50an6xy06r6n/hotswap_pcb_generator/img/gallery/pcb_composite.png

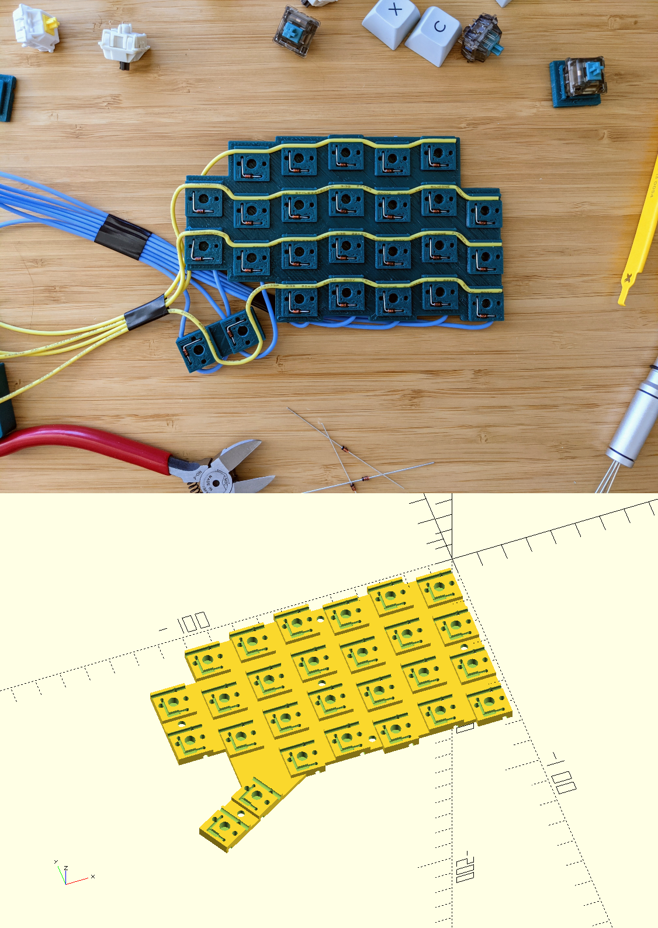
img/gallery/pcb_composite.png
