50an6xy06r6n/hotswap_pcb_generator/img/gallery/solid_case.jpg

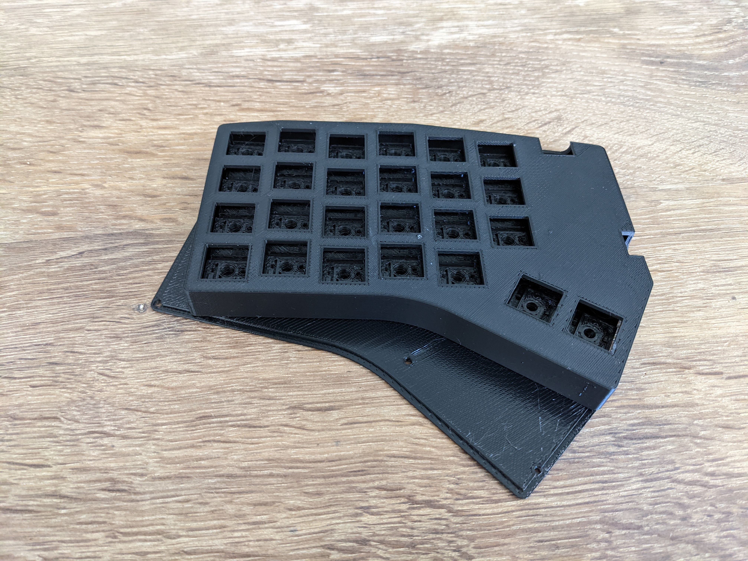
img/gallery/solid_case.jpg
