50an6xy06r6n/hotswap_pcb_generator/img/gallery/stabilizer.jpg

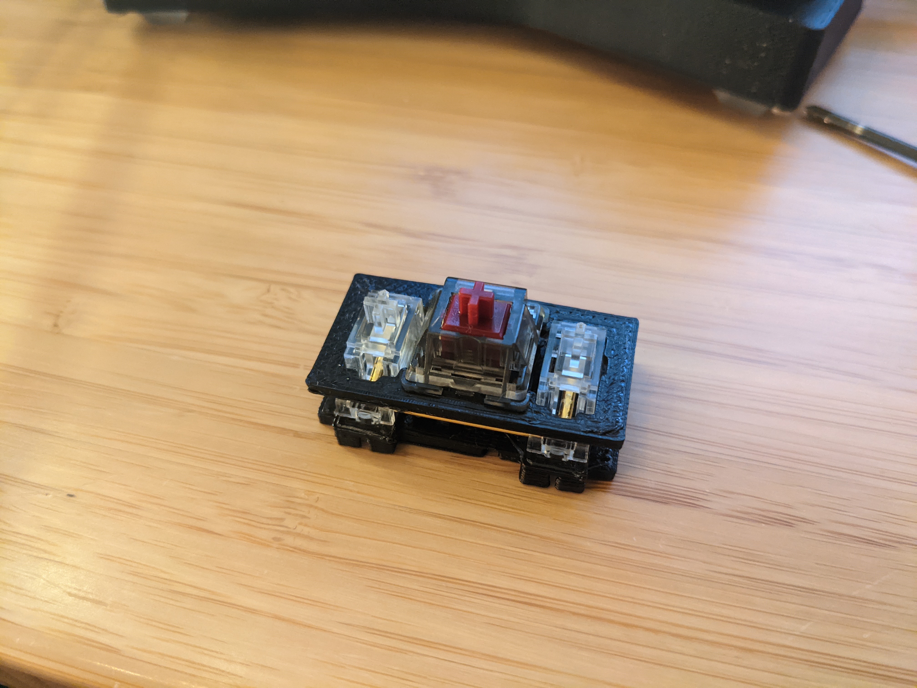
img/gallery/stabilizer.jpg
