50an6xy06r6n/hotswap_pcb_generator/stl/individual_components/mx_socket_improved.stl

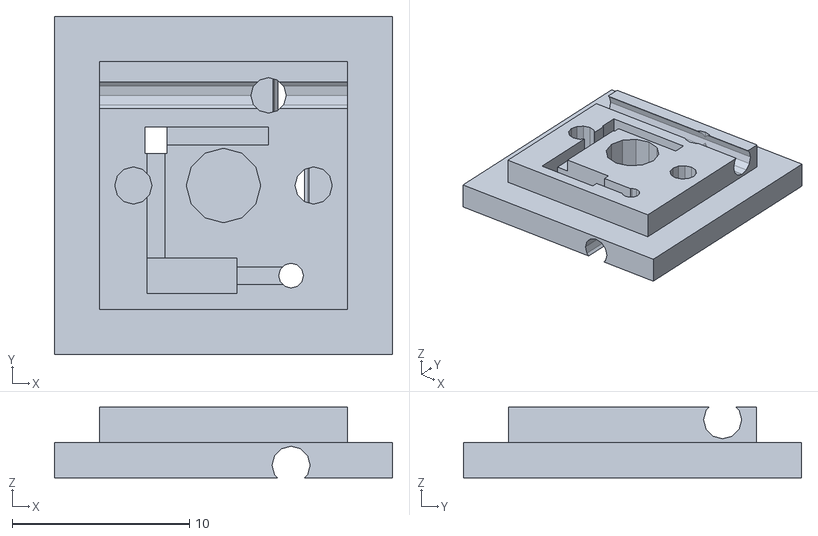
[picture p26: CAD file, 2021-07-27]
stl/individual_components/mx_socket_improved.stl
19.1 x 19.1 x 4.00
