50an6xy06r6n/hotswap_pcb_generator/stl/individual_components/choc_switch.stl

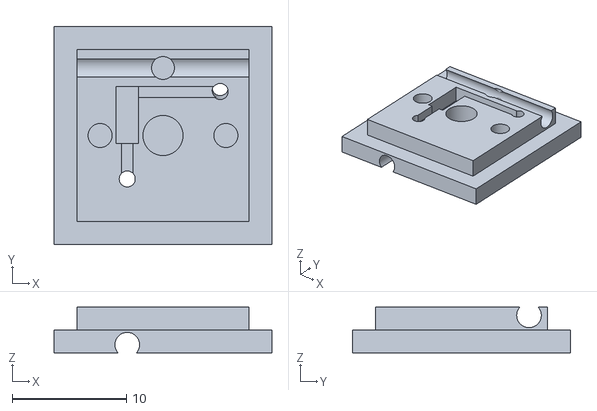
[picture p27: CAD file, 2021-07-27]
stl/individual_components/choc_switch.stl
19.1 x 19.1 x 4.00
