50an6xy06r6n/hotswap_pcb_generator/stl/individual_components/trrs.stl

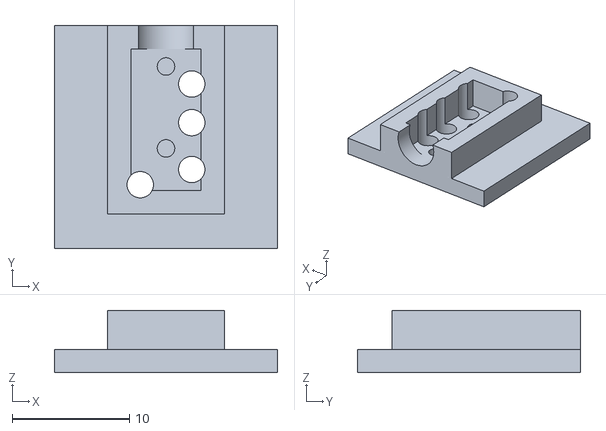
[picture p28: CAD file, 2021-07-27]
stl/individual_components/trrs.stl
19.1 x 19.1 x 5.33
