50an6xy06r6n/hotswap_pcb_generator/scad/diode_bending_template.scad

include <parameters.scad>

module mx_improved_diode_template() {
    difference() {
        translate([0,0,-diode_foldover/2-0.5])
            cube([socket_size, socket_size, pcb_thickness+diode_foldover], center=true);
            
        // Bottom switch pin
        translate([-3*mx_schematic_unit,2*mx_schematic_unit,0])
            translate([0,socket_size/2-0.75,0])
                cube([1,socket_size,pcb_thickness+diode_foldover*2+2],center=true);
        // Diode cathode cutout
        translate([3*mx_schematic_unit,-4*mx_schematic_unit,0])
            translate([socket_size/2-0.001,0,0])
                cube([socket_size,1,pcb_thickness+diode_foldover*2+2],center=true);

        // Diode Channel
        translate([-3*mx_schematic_unit,-1*mx_schematic_unit-.25,pcb_thickness/2])
            cube([1,6*mx_schematic_unit+.5,2],center=true);
        translate([0,-4*mx_schematic_unit,pcb_thickness/2])
           cube([6*mx_schematic_unit,1,2],center=true);
        translate([-1*mx_schematic_unit-.5,-4*mx_schematic_unit,pcb_thickness/2])
            cube([4*mx_schematic_unit,2,3],center=true);
        
        translate([-1.5*mx_schematic_unit,2*mx_schematic_unit,pcb_thickness/2])
            cube([3*mx_schematic_unit,1,2],center=true);


        translate([-mx_schematic_unit-0.5,5*mx_schematic_unit,0]) rotate([0,0,90]) {
            // Bottom switch pin
            translate([-3*mx_schematic_unit,2*mx_schematic_unit,0])
                translate([0,-0.5,0])
                    cube([1,1,pcb_thickness+7],center=true);

            // Diode Channel
            translate([-3*mx_schematic_unit,-1*mx_schematic_unit-.25,pcb_thickness/2])
                cube([1,6*mx_schematic_unit+.5,2],center=true);
            translate([0,-4*mx_schematic_unit,pcb_thickness/2])
               cube([6*mx_schematic_unit,1,2],center=true);
            translate([-1*mx_schematic_unit-.5,-4*mx_schematic_unit,pcb_thickness/2])
                cube([4*mx_schematic_unit,2,3],center=true);

        }
     }
}

module mx_diode_template() {
    difference() {
        cube([socket_size, socket_size, pcb_thickness], center=true);
            
        // Bottom switch pin
        translate([-3*mx_schematic_unit,2*mx_schematic_unit,0])
            translate([0,socket_size/2-0.001,0])
                cube([1,socket_size,pcb_thickness+1],center=true);
        // Diode cathode cutout
        translate([3*mx_schematic_unit,-4*mx_schematic_unit,0])
            translate([socket_size/2-0.001,0,0])
                cube([socket_size,1,pcb_thickness+1],center=true);

        // Diode Channel
        translate([-3*mx_schematic_unit,-1*mx_schematic_unit-.25,pcb_thickness/2])
            cube([1,6*mx_schematic_unit+.5,2],center=true);
        translate([0,-4*mx_schematic_unit,pcb_thickness/2])
            cube([6*mx_schematic_unit,1,2],center=true);
        translate([-1*mx_schematic_unit-.5,-4*mx_schematic_unit,pcb_thickness/2])
            cube([4*mx_schematic_unit,2,3],center=true);
    }
}

module choc_diode_template() {
    difference() {
        cube([socket_size, socket_size, pcb_thickness], center=true);
            
        // Bottom switch pin
        translate([5,3.8,0])
            translate([socket_size/2-0.001,0,0])
                cube([socket_size,1,pcb_thickness+1],center=true);
        // Diode cathode cutout
        translate([-3.125,-3.8,0])
            translate([0,-socket_size/2+0.001,0])
                cube([1,socket_size,pcb_thickness+1],center=true);

        // Diode Channel
        translate([-3.125,0,pcb_thickness/2])
            cube([1,7.6,2],center=true);
        translate([.75,3.8,pcb_thickness/2])
            cube([8.5,1,2],center=true);
        translate([-3.125,1.8,pcb_thickness/2])
            cube([2,5,3.5],center=true);
    }
}

if (switch_type == "mx") {
    if (use_folded_contact) {
        mx_improved_diode_template();
    } else {
        mx_diode_template();
    }        
} else if (switch_type == "choc") {
    choc_diode_template();
} else {
    assert(false, "switch_type is invalid");
}
