50an6xy06r6n/hotswap_pcb_generator/scad/plate.scad

include <parameters.scad>
include <param_processing.scad>

use <switch.scad>
use <mcu.scad>
use <trrs.scad>
use <stabilizer.scad>
use <standoff.scad>
use <pcb.scad>

function plate_borders(borders, h_unit=1, v_unit=1) = [
    borders[0] + plate_margin/v_unit,
    borders[1] + plate_margin/v_unit,
    borders[2] + plate_margin/h_unit,
    borders[3] + plate_margin/h_unit,
];

// Generates a 2-D profile of the switch plate, which forms the basis for all case forms
module plate_footprint(
    switch_layout,
    mcu_layout,
    trrs_layout,
    plate_layout,
    stab_layout
) {
    scale_factor = use_plate_layout_only
        ? plate_precision * 100000
        : 1;

    // Create inner fillets
    offset(-plate_inner_fillet,$fn=360)
    offset(delta=plate_inner_fillet)

    // Create outer fillets
    offset(plate_outer_fillet,$fn=360)
    offset(delta=-plate_outer_fillet)

    // Offset plate margin and do scale-based fudging to merge points (deprecated)
    scale(scale_factor)
    offset(delta=plate_margin / scale_factor)
    scale(1/scale_factor)

    // Base plate layout containing board components
    {
        if (use_plate_layout_only) {
            plate_layout_footprint(plate_layout);
        } else {
            // Do a basic hull of all components to make sure they fit
            hull() {
                pcb_footprint(
                    switch_layout,
                    mcu_layout,
                    trrs_layout,
                    stab_layout
                );

                // Add plate layout data as well
                plate_layout_footprint(plate_layout);
            }
        }
    }
}

// Helper module to generate the base form of the plate_layout data
module plate_layout_footprint(plate_layout) {
    // Trim outer edge of the plate to clean up the profile
    difference() {
        // Hull each group and then union separately, which allows for concavity
        union() for (group = plate_layout) {
            hull() {
                layout_pattern(group) {
                    let(component_type = $extra_data[0]) {
                        if (component_type == "switch")
                            switch_footprint($borders);
                        else if (component_type == "mcu"){
                            mcu_footprint($borders);}
                        else if (component_type == "trrs")
                            trrs_footprint($borders);
                        else if (component_type == "stab")
                            stabilizer_footprint($borders, $extra_data[1]);
                    }
                }
            }
        }

        // Generate a negative external profile of the plate (useful for cleaning up convex intersections)
        union() for (group = plate_layout) {
            layout_pattern(group) {
                let(component_type = $extra_data[0]) {
                    if (component_type == "switch")
                        switch_footprint_trim($borders, $trim);
                    else if (component_type == "mcu"){
                        mcu_footprint_trim($borders, $trim);}
                    else if (component_type == "trrs")
                        trrs_footprint_trim($borders, $trim);
                    else if (component_type == "stab")
                        stabilizer_footprint_trim($borders, $extra_data[1], $trim);
                }
            }
        }
    }
}

// Extruded version of the plate footprint with optional offset
module plate_base(
    switch_layout,
    mcu_layout,
    trrs_layout,
    plate_layout,
    stab_layout,
    thickness=plate_thickness,
    offset=0
) {
    linear_extrude(thickness, center=true, convexity=10)
        offset(offset)
        plate_footprint(
            switch_layout,
            mcu_layout,
            trrs_layout,
            plate_layout,
            stab_layout
        );
}

// Creates a standalone plate with cutouts and optional standoffs
module plate(
    switch_layout,
    mcu_layout,
    trrs_layout,
    plate_layout,
    stab_layout,
    standoff_layout
) {
    difference() {
        union() {
            plate_base(
                switch_layout,
                mcu_layout,
                trrs_layout,
                plate_layout,
                stab_layout,
                plate_thickness
            );
            layout_pattern(standoff_layout) {
                plate_standoff($extra_data);
            }
        }

        // Add component cutouts
        layout_pattern(switch_layout) {
            switch_plate_cutout();
        }
        layout_pattern(mcu_layout) {
            mcu_plate_cutout();
        }
        layout_pattern(trrs_layout) {
            trrs_plate_cutout();
        }
        layout_pattern(stab_layout) {
            stabilizer_plate_cutout($extra_data);
        }
        layout_pattern(standoff_layout) {
            plate_standoff_hole($extra_data);
        }

        // Additional user-defined cutouts
        linear_extrude(plate_thickness+1, center=true)
        intersection() {
            // Make sure it doesn't cut into the case walls by intersecting with the inner plate profile
            offset(-case_wall_thickness)
                plate_footprint(switch_layout, mcu_layout, trrs_layout, plate_layout, stab_layout);
            additional_plate_cutouts(); 
        }
    }
}

plate(
    switch_layout_final,
    mcu_layout_final,
    trrs_layout_final,
    plate_layout_final,
    stab_layout_final,
    standoff_layout_final
);
// plate_footprint(
//     switch_layout_final,
//     mcu_layout_final,
//     trrs_layout_final,
//     plate_layout_final
// );
