50an6xy06r6n/hotswap_pcb_generator/scad/stabilizer.scad

include <parameters.scad>
include <param_processing.scad>
include <stabilizer_spacing.scad>

use <switch.scad>


module stabilizer_layout(spacing=stab_2u) {
    switch_offset = len(spacing) == 4
        ? spacing[3]
        : 0;
    center_x = spacing[0]*unit/2 + switch_offset;
    translate([unit/2-center_x,0,0]) {
        translate([center_x-spacing[1],0,0]) children();
        translate([center_x+spacing[2],0,0]) mirror([1,0,0]) children();
    }
}

module stabilizer_pcb(spacing=stab_2u) {
    margin = (spacing[0]-1)/2;
    difference() {
        union() {
            stabilizer_pcb_base([1,2,0,0], spacing);
            switch_socket_base([1,1,1+margin*unit*mm,1+margin*unit*mm]);
        }
        stabilizer_pcb_cutout(spacing);
        switch_socket_cutout([1,1,1+margin*unit*mm,1+margin*unit*mm]);
    }
}

module stabilizer_plate(spacing=stab_2u, thickness=plate_thickness) {
    linear_extrude(thickness, center=true)
    difference() {
        stabilizer_footprint([1,1,1,1], spacing);
        stabilizer_plate_cutout_footprint(spacing);
        switch_plate_cutout_footprint();
    }
}


module stabilizer_pcb_base(borders=[1,2,0,0], spacing=stab_2u) {
    module single_base() {
        translate([0,-v_unit/2,0])
            border(
                [7.5,1*unit],
                [borders[0]-1,max(borders[1]-1,1),0,0],
                pcb_thickness,
                h_border_width,
                v_border_width
            );
    }
    stabilizer_layout(spacing)
        single_base();
}

module stabilizer_pcb_cutout(spacing=stab_2u) {
    module pcb_mount_cutout() {
        translate([0,-v_unit/2,-pcb_thickness/2]) {
            translate([0,6.985,0]) {
                cylinder(d=3.5, h=pcb_thickness+1);
                translate([0,0,-2.5]) cylinder(d=4, h=pcb_thickness);
            }
            translate([0,-8.255,0]) {
                bottom_cutout_diameter = 4.5;
                translate([0,0,-0.5]) hull() {
                    cylinder(d=bottom_cutout_diameter, h=pcb_thickness+1);
                    translate([-bottom_cutout_diameter/2,-bottom_cutout_diameter/2,0]) cube([bottom_cutout_diameter,bottom_cutout_diameter/2,pcb_thickness+1]);
                }
                translate([0,0,-1.2]) hull() {
                    cylinder(d=bottom_cutout_diameter, h=pcb_thickness);
                    translate([0,-1,0]) cylinder(d=bottom_cutout_diameter, h=pcb_thickness);
                }
            }
        }
    }
    module plate_mount_cutout() {
        // Nothing needs to be done on the PCB
    }
    stabilizer_layout(spacing) {
        if (stabilizer_type == "pcb") {
            pcb_mount_cutout();
        } else if (stabilizer_type == "plate") {
            plate_mount_cutout();
        } else {
            assert(false, "stabilizer_type is invalid");
        }
    }
    translate([0,0,-pcb_thickness-eps])
    linear_extrude(pcb_thickness+2*eps)
        trrs_footprint_trim(borders, trim);
}


module stabilizer_footprint(borders=[1,1,1,1], spacing=stab_2u) {
    translate([unit/2,-v_unit/2,0])
    border_footprint(
        [spacing[0]*h_unit,v_unit],
        [for (b=borders) b-1]
    );
}

module stabilizer_footprint_trim(borders=[1,1,1,1], spacing=stab_2u, trim=undef) {
    if (trim)
    translate([unit/2,-v_unit/2,0])
    border_trim(
        [spacing[0]*h_unit,v_unit],
        [for (b=borders) b-1],
        trim
    );
}

module stabilizer_plate_cutout_footprint(spacing=stab_2u) {
    module pcb_mount_cutout() {
        // Same profile works for both
        plate_mount_cutout();
    }
    module plate_mount_cutout() {
        total_width = spacing[1] + spacing[2];
        wire_cutout_width = spacing == stab_2u
            ? unit/2
            : unit/4;
        translate([0,-v_unit/2,0]) {
            translate([-3.6,-6.604,0]) square([7.2, 12.2936]);
            translate([-1.524,-7.7724,0]) square([3.048, 2]);
            translate([-4.191,-0.508,0]) square([4.191, 2.794]);
            translate([0,-wire_cutout_width/2,0]) square([total_width, wire_cutout_width]);
        }
    }
    stabilizer_layout(spacing) {
        if (stabilizer_type == "pcb") {
            pcb_mount_cutout();
        } else if (stabilizer_type == "plate") {
            plate_mount_cutout();
        } else {
            assert(false, "stabilizer_type is invalid");
        }
    }
}


module stabilizer_plate_base(borders=[1,1,1,1], spacing=stab_2u, thickness=plate_thickness) {
    linear_extrude(thickness, center=true)
        stabilizer_footprint(borders, spacing);
}

module stabilizer_plate_cutout(spacing=stab_2u, thickness=plate_thickness) {
    linear_extrude(thickness+1, center=true)
        stabilizer_plate_cutout_footprint(spacing);
}

stabilizer_pcb(stab_2u);
//stabilizer_plate(stab_2u);
