50an6xy06r6n/hotswap_pcb_generator/img/build_guide/00_case_pieces.JPG

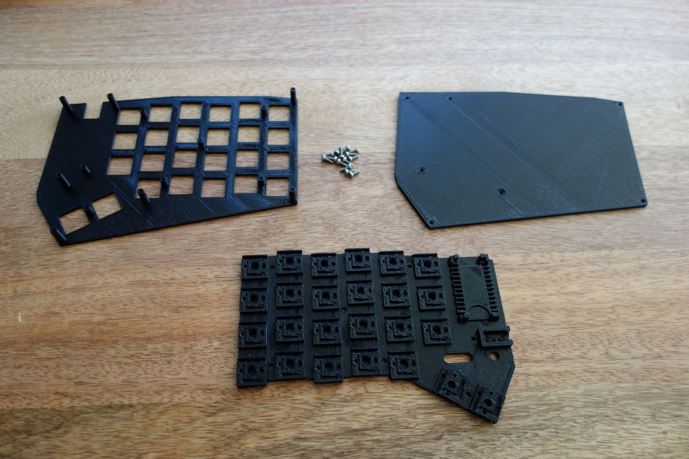
img/build_guide/00_case_pieces.JPG
