50an6xy06r6n/hotswap_pcb_generator/img/build_guide/09_all_wires.JPG

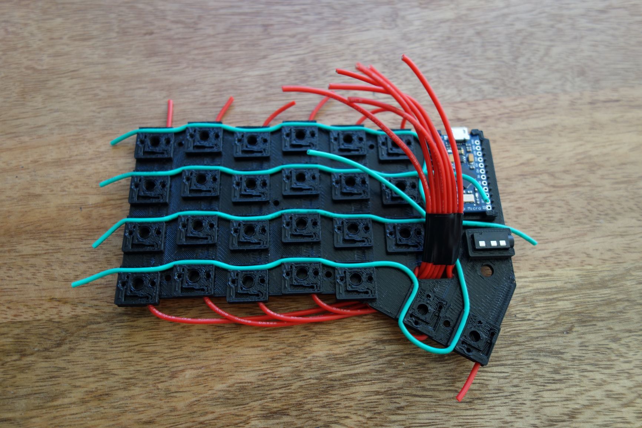
img/build_guide/09_all_wires.JPG
