50an6xy06r6n/hotswap_pcb_generator/img/build_guide/15_diode_template.JPG

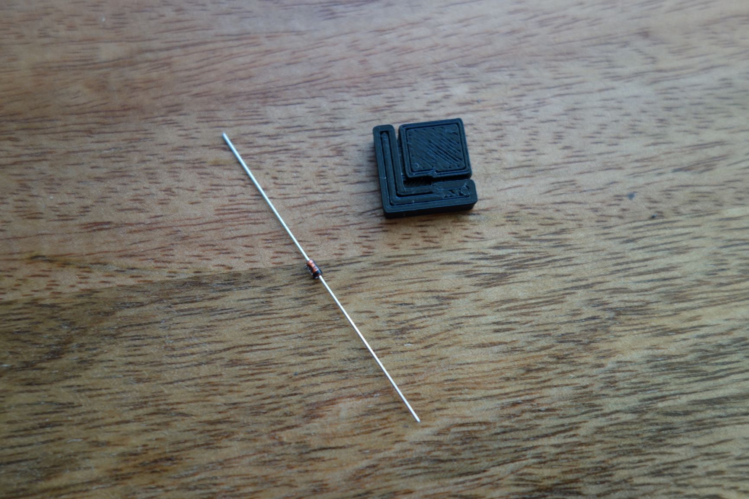
img/build_guide/15_diode_template.JPG
